d-el/LampOne/Photo/IMG_7622.jpg

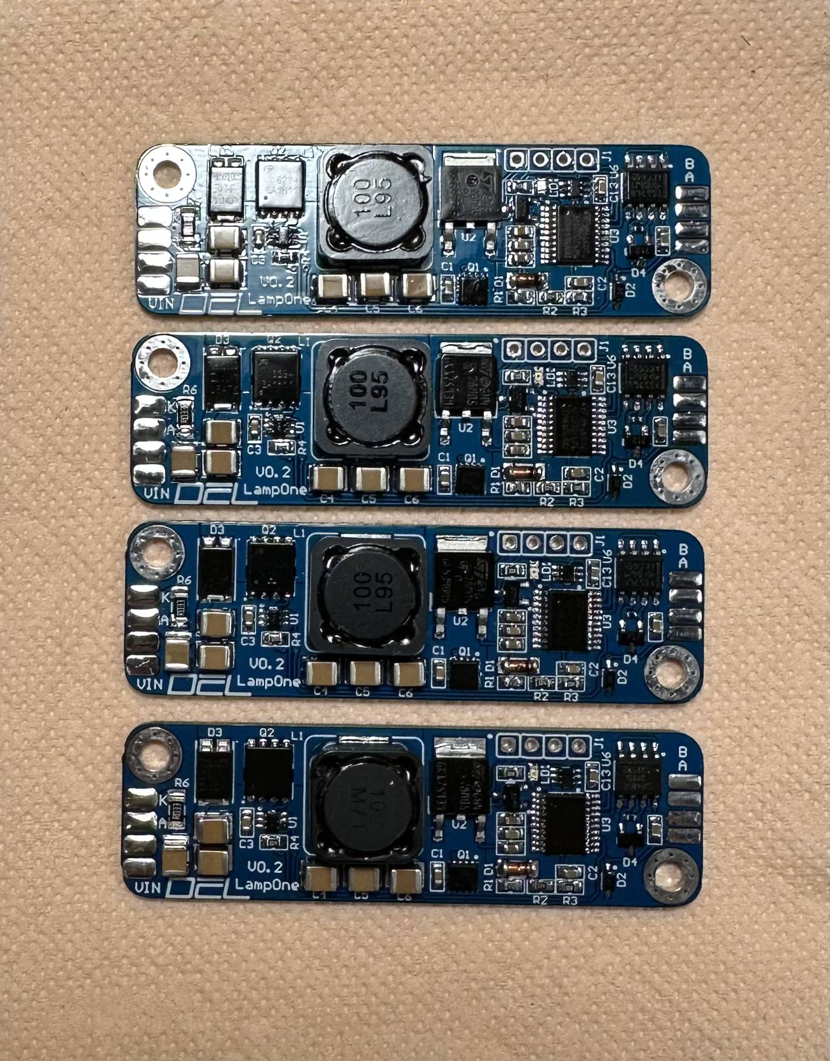
Photo/IMG_7622.jpg
