d-el/LampOne/Photo/IMG_7627.jpg

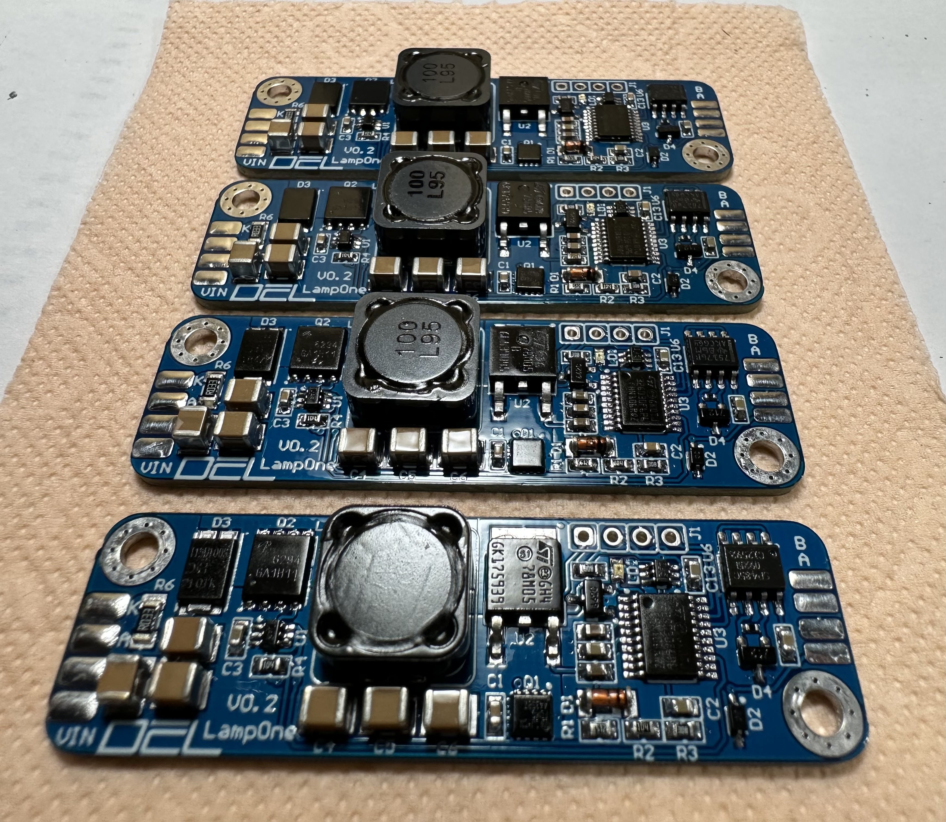
Photo/IMG_7627.jpg
