d-el/LampOne/FW/task/include/systemTSK.h

/*!****************************************************************************
 * @file		systemTSK.h
 * @author		Storozhenko Roman - D_EL
 * @version		V1.0
 * @date		11.05.2022
 * @copyright 	The MIT License (MIT). Copyright (c) 2022 Storozhenko Roman
 */
#ifndef systemTSK_H
#define systemTSK_H

/*!****************************************************************************
* Include
*/

/*!****************************************************************************
* User define
*/
#define SYSTEM_TSK_PERIOD	(10)	///<[ms]

/*!****************************************************************************
* Prototypes for the functions
*/
void OSinit(void);

#endif //systemTSK_H
/******************************** END OF FILE ********************************/
